Synthron/SymAsym/Hardware/Black_Devil/black_devil.kicad_pcb

## KiCad design Hardware/Black_Devil/black_devil.kicad_pcb (2023-11-16)

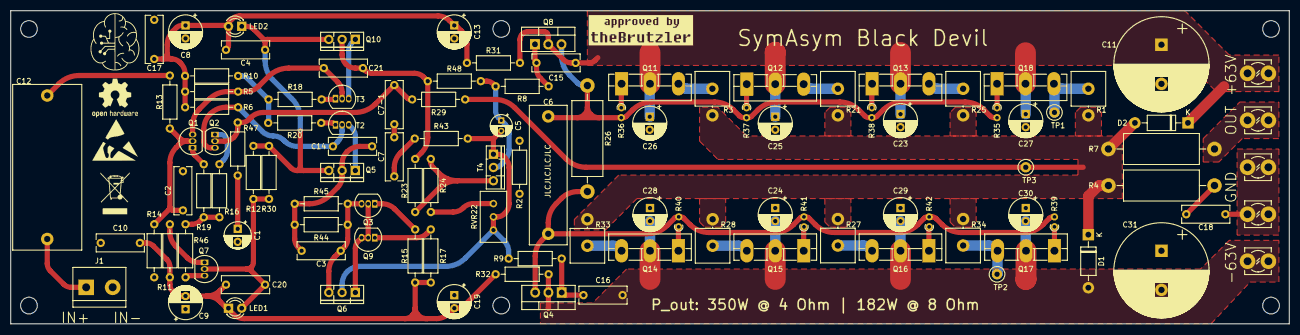
[picture p6: board black_devil.kicad_pcb from above]

Board: 2 copper layers, 245.0 x 60.0 mm, 113 parts (0 on the bottom side), 60 nets.

Parts:
C1: 330µF/16V; CP_Radial_D5.0mm_P2.50mm
C2: 680p; C_Rect_L9.0mm_W3.2mm_P7.50mm_MKT
C3, C4, C10, C17, C20: 100n; C_Rect_L9.0mm_W3.2mm_P7.50mm_MKT
C5: 47µ/25V; CP_Radial_D4.0mm_P2.00mm
C6: 680n; C_Rect_L26.5mm_W7.0mm_P22.50mm_MKS4
C7, C7-1: 10p; C_Rect_L9.0mm_W3.2mm_P7.50mm_MKT
C8, C9, C13, C19, C23, C24, C25, C26, C27, C28, C29, C30: 22µ 100V; CP_Radial_D6.3mm_P2.50mm
C11, C31: 680µ 100V; CP_Radial_D18.0mm_P7.50mm
C12: 10µ; C_Rect_L31.5mm_W13.0mm_P27.50mm_MKS4
C14, C15, C16, C21: 100p; C_Rect_L9.0mm_W3.2mm_P7.50mm_MKT
C18: 47n; C_Rect_L9.0mm_W3.2mm_P7.50mm_MKT
D1, D2: 1N4004; D_DO-41_SOD81_P10.16mm_Horizontal
J1: Input; TerminalBlock_bornier-2_P5.08mm
J3: OUT; TerminalBlock_MetzConnect_360381_1x01_Horizontal_ScrewM3.0
J4: +63V; TerminalBlock_MetzConnect_360381_1x01_Horizontal_ScrewM3.0
J5: -63V; TerminalBlock_MetzConnect_360381_1x01_Horizontal_ScrewM3.0
J6: GND; TerminalBlock_MetzConnect_360381_1x01_Horizontal_ScrewM3.0
J7: SPK_GND; TerminalBlock_MetzConnect_360381_1x01_Horizontal_ScrewM3.0
LED1: RED; LED_D3.0mm
LED2: BLUE; LED_D3.0mm
Q1, Q2, Q3, Q7, Q9: 2N5551; TO-92_Inline
Q4: MJE15031; TO-220-3_Vertical
Q5, Q10: MJE350; TO-126-3_Vertical
Q6: MJE340; TO-126-3_Vertical
Q8: MJE15030; TO-220-3_Vertical
Q11, Q12, Q13, Q18: MJL3281; TO-3PB-3_Vertical
Q14, Q15, Q16, Q17: MJL1302; TO-3PB-3_Vertical
R1, R3, R21, R25, R27, R28, R33, R34: 0R22 5W; R_Axial_Power_L20.0mm_W6.4mm_P5.08mm_Vertical
R2: 10; R_Axial_DIN0207_L6.3mm_D2.5mm_P10.16mm_Horizontal
R4: 4R7 2W; R_Axial_DIN0614_L14.3mm_D5.7mm_P20.32mm_Horizontal
R5, R6: 1k; R_Axial_DIN0207_L6.3mm_D2.5mm_P10.16mm_Horizontal
R7: 10 2W; R_Axial_DIN0614_L14.3mm_D5.7mm_P20.32mm_Horizontal
R8, R9, R18, R20: 22; R_Axial_DIN0207_L6.3mm_D2.5mm_P10.16mm_Horizontal
R10: 120; R_Axial_DIN0207_L6.3mm_D2.5mm_P10.16mm_Horizontal
R11: 390; R_Axial_DIN0207_L6.3mm_D2.5mm_P10.16mm_Horizontal
R12, R30: 68k; R_Axial_DIN0207_L6.3mm_D2.5mm_P10.16mm_Horizontal
R13: 680; R_Axial_DIN0207_L6.3mm_D2.5mm_P10.16mm_Horizontal
R14, R29, R45: 22k; R_Axial_DIN0207_L6.3mm_D2.5mm_P10.16mm_Horizontal
R15, R17: 100; R_Axial_DIN0207_L6.3mm_D2.5mm_P10.16mm_Horizontal
R16, R19, R31, R32: 47; R_Axial_DIN0207_L6.3mm_D2.5mm_P10.16mm_Horizontal
R23: 1k5; R_Axial_DIN0207_L6.3mm_D2.5mm_P10.16mm_Horizontal
R24: 270; R_Axial_DIN0207_L6.3mm_D2.5mm_P10.16mm_Horizontal
R26: 68 2W; R_Axial_DIN0614_L14.3mm_D5.7mm_P20.32mm_Horizontal
R35, R36, R37, R38, R39, R40, R41, R42: 4R7; R_Axial_DIN0204_L3.6mm_D1.6mm_P1.90mm_Vertical
R43: 470; R_Axial_DIN0207_L6.3mm_D2.5mm_P10.16mm_Horizontal
R44: 15k; R_Axial_DIN0207_L6.3mm_D2.5mm_P10.16mm_Horizontal
R46: 10k; R_Axial_DIN0207_L6.3mm_D2.5mm_P10.16mm_Horizontal
R47: 820; R_Axial_DIN0207_L6.3mm_D2.5mm_P10.16mm_Horizontal
R48: 15; R_Axial_DIN0207_L6.3mm_D2.5mm_P10.16mm_Horizontal
RVR22: 500; Potentiometer_Bourns_3296W_Vertical
T2, T3: 2N5401; TO-92_Inline
T4: BD139; TO-126-3_Vertical
TP1: MP1; TestPoint_Loop_D2.50mm_Drill1.0mm
TP2, TP3: MP2; TestPoint_Loop_D2.50mm_Drill1.0mm

Connections:
+VDC: C11.1, C15.1, C23.1, C25.1, C26.1, C27.1, D2.1 (K), J4.1, Q8.2 (C), Q11.2 (C), Q12.2 (C), Q13.2 (C), Q18.2 (C), R31.2
-VDC: C16.2, C24.2, C28.2, C29.2, C30.2, C31.2, D1.2 (A), J5.1, Q4.2 (C), Q14.2 (C), Q15.2 (C), Q16.2 (C), Q17.2 (C), R32.2
/out: J3.1, R7.2
GND: C11.2, C18.2, C23.2, C24.1, C25.2, C26.2, C27.2, C28.1, C29.1, C30.1, C31.1, J6.1, J7.1, R2.2
GNDA: C1.2, C2.2, C8.2, C9.1, C10.1, C13.2, C17.2, C19.1, J1.2, R2.1, R14.2
unnamed: C1.1, R47.1
unnamed: C7.1, C7-1.2
unnamed: C7.2, R43.1
unnamed: C12.2, R13.1
unnamed: C18.1, R4.2
unnamed: D1.1 (K), D2.2 (A), R1.2, R3.2, R4.1, R7.1, R21.2, R25.2, R27.2, R28.2, R29.2, R33.2, R34.2, TP3.1
unnamed: C12.1, J1.1
unnamed: C20.1, LED1.2 (A), Q7.2 (B), R12.2, R30.2
unnamed: C9.2, C10.2, C19.2, C20.2, LED1.1 (K), R11.2, R15.2, R17.2, R32.1
unnamed: C4.1, C8.1, C13.1, C17.1, LED2.2 (A), R5.1, R6.1, R10.1, R31.1
unnamed: C4.2, LED2.1 (K), Q5.3 (B), Q10.3 (B), R12.1, R30.1
unnamed: C2.1, Q1.2 (B), R13.2, R14.1
unnamed: C21.1, Q1.3 (C), R5.2, T3.2 (B)
unnamed: Q1.1 (E), R19.1
unnamed: C7-1.1, Q2.2 (B), R29.1, R47.2
unnamed: C14.1, Q2.3 (C), R6.2, T2.2 (B)
unnamed: Q2.1 (E), R16.1
unnamed: Q3.2 (B), Q6.1 (E), Q9.2 (B), Q9.3 (C)
unnamed: C3.2, Q3.3 (C), Q6.3 (B), R44.2, R45.2
unnamed: Q3.1 (E), R15.1
unnamed: C16.1, Q4.1 (B), R9.2
unnamed: C6.2, Q4.3 (E), R26.2, R39.2, R40.2, R41.2, R42.2
unnamed: C3.1, C14.2, Q5.2 (C), R44.1, R45.1
unnamed: Q5.1 (E), T2.3 (C)
unnamed: C5.2, Q6.2 (C), R9.1, R43.2, RVR22.2, RVR22.3, T4.1 (E)
unnamed: Q7.3 (C), R46.2
unnamed: Q7.1 (E), R11.1
unnamed: C15.2, Q8.1 (B), R8.1
unnamed: C6.1, Q8.3 (E), R26.1, R35.2, R36.2, R37.2, R38.2
unnamed: Q9.1 (E), R17.1
unnamed: C21.2, Q10.2 (C), R23.1, R48.1
unnamed: Q10.1 (E), T3.3 (C)
unnamed: Q11.1 (B), R36.1
unnamed: Q11.3 (E), R3.1
unnamed: Q12.1 (B), R37.1
unnamed: Q12.3 (E), R21.1
unnamed: Q13.1 (B), R38.1
unnamed: Q13.3 (E), R25.1
unnamed: Q14.1 (B), R40.1
unnamed: Q14.3 (E), R33.1
unnamed: Q15.1 (B), R41.1
unnamed: Q15.3 (E), R28.1
unnamed: Q16.1 (B), R42.1
unnamed: Q16.3 (E), R27.1
unnamed: Q17.1 (B), R39.1
unnamed: Q17.3 (E), R34.1, TP2.1
unnamed: Q18.1 (B), R35.1
unnamed: Q18.3 (E), R1.1, TP1.1
unnamed: R10.2, R18.1, R20.2
unnamed: R16.2, R19.2, R46.1
unnamed: R24.2, RVR22.1
unnamed: R20.1, T2.1 (E)
unnamed: R18.2, T3.1 (E)
unnamed: R23.2, R24.1, T4.3 (B)
unnamed: C5.1, R8.2, R48.2, T4.2 (C)
