Synthron/SymAsym/Hardware/Black_Devil/Softstart.kicad_pcb

## KiCad design Hardware/Black_Devil/Softstart.kicad_pcb (2023-11-16)

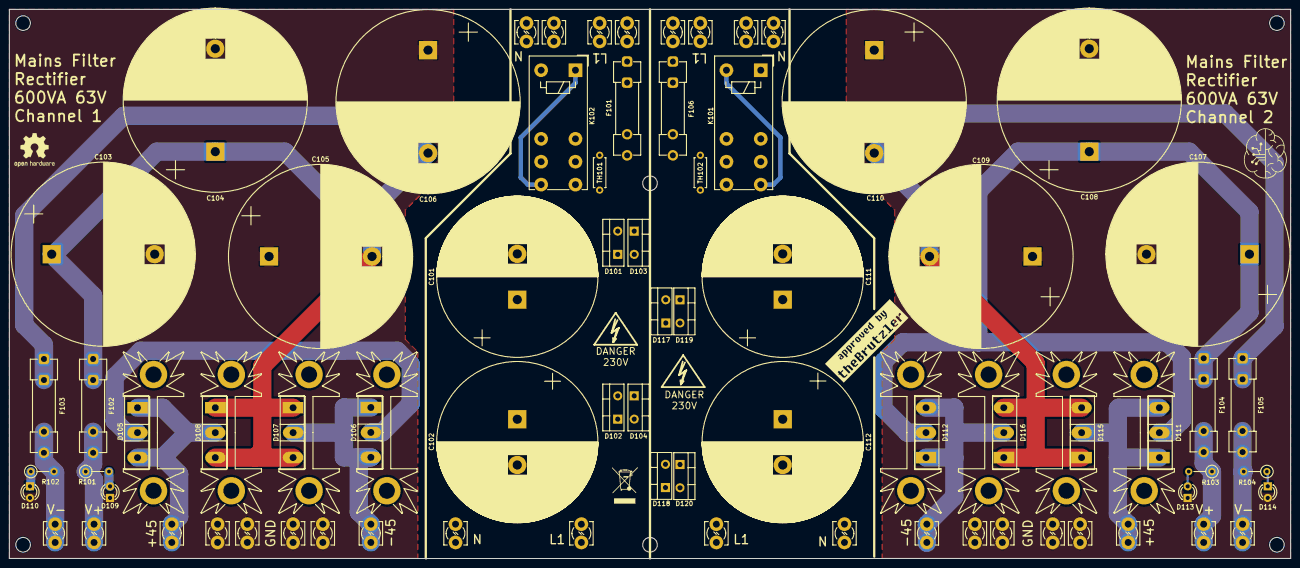
[picture p7: board Softstart.kicad_pcb from above]

Board: 2 copper layers, 280.0 x 120.0 mm, 82 parts (0 on the bottom side), 30 nets.

Parts:
C101, C102, C111, C112: 22.000µ 40V; CP_Radial_D35.0mm_P10.00mm_SnapIn
C103, C104, C105, C106, C107, C108, C109, C110: 10.000µ 80V; CP_Radial_D40.0mm_P22,5
D101, D102, D103, D104, D117, D118, D119, D120: MUR860; TO-220-2_Vertical
D105, D106, D107, D108, D111, D112, D115, D116: MUR3020; TO-247-3_Vertical
D109, D110, D113, D114: LED; LED_D3.0mm
F101, F106: 3,15A; Fuseholder_Clip-5x20mm_Littelfuse_100_Inline_P20.50x4.60mm_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
F102, F103, F104, F105: 8A; Fuseholder_Clip-5x20mm_Littelfuse_100_Inline_P20.50x4.60mm_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
HS101, HS102, HS103, HS104, HS105, HS106, HS107, HS108: SK104; Heatsink_Fischer_SK104-STCB_35x13mm__2xDrill3.5mm_ScrewM3
J101, J113, J123, J125: L1; TerminalBlock_MetzConnect_360381_1x01_Horizontal_ScrewM3.0
J102, J104, J114, J126, J127, J128: N; TerminalBlock_MetzConnect_360381_1x01_Horizontal_ScrewM3.0
J103, J124: L1_F; TerminalBlock_MetzConnect_360381_1x01_Horizontal_ScrewM3.0
J105, J116: +45VAC; TerminalBlock_MetzConnect_360381_1x01_Horizontal_ScrewM3.0
J106, J119: -45VAC; TerminalBlock_MetzConnect_360381_1x01_Horizontal_ScrewM3.0
J107, J108, J120, J121: 0V; TerminalBlock_MetzConnect_360381_1x01_Horizontal_ScrewM3.0
J109, J115: +63VDC; TerminalBlock_MetzConnect_360381_1x01_Horizontal_ScrewM3.0
J110, J122: -63VDC; TerminalBlock_MetzConnect_360381_1x01_Horizontal_ScrewM3.0
J111, J112, J117, J118: GND; TerminalBlock_MetzConnect_360381_1x01_Horizontal_ScrewM3.0
K101, K102: FINDER-40.52; Relay_DPDT_Finder_40.52
R101, R102, R103, R104: 4k7 1W; R_Axial_DIN0207_L6.3mm_D2.5mm_P5.08mm_Vertical
TH101, TH102: EPC B57364-S100; R_Axial_DIN0207_L6.3mm_D2.5mm_P7.62mm_Horizontal

Connections:
GND1: C103.2, C104.2, C105.1, C106.1, D109.1 (K), D110.2 (A), J107.1, J108.1, J111.1, J112.1
GND2: C107.2, C108.2, C109.1, C110.1, D113.1 (K), D114.2 (A), J117.1, J118.1, J120.1, J121.1
unnamed: C105.2, C106.2, D107.1 (A), D107.3 (A), D108.1 (A), D108.3 (A), F103.1
unnamed: C109.2, C110.2, D115.1 (A), D115.3 (A), D116.1 (A), D116.3 (A), F105.1
unnamed: C101.2, D101.2 (A), D103.1 (K), K102.14, K102.24, K102.A1, TH101.1
unnamed: C101.1, C102.1, D101.1 (K), D102.2 (A), D103.2 (A), D104.1 (K)
unnamed: C102.2, D102.1 (K), D104.2 (A), J103.1
unnamed: C103.1, C104.1, D105.2 (K), D106.2 (K), F102.1
unnamed: D106.1 (A), D106.3 (A), D107.2 (K), J106.1
unnamed: D105.1 (A), D105.3 (A), D108.2 (K), J105.1
unnamed: D109.2 (A), R101.2
unnamed: D110.1 (K), R102.1
unnamed: C107.1, C108.1, D111.2 (K), D112.2 (K), F104.1
unnamed: D113.2 (A), R103.2
unnamed: D114.1 (K), R104.1
unnamed: D111.1 (A), D111.3 (A), D115.2 (K), J116.1
unnamed: D112.1 (A), D112.3 (A), D116.2 (K), J119.1
unnamed: C111.2, D117.2 (A), D119.1 (K), K101.14, K101.24, K101.A2, TH102.1
unnamed: C111.1, C112.1, D117.1 (K), D118.2 (A), D119.2 (A), D120.1 (K)
unnamed: C112.2, D118.1 (K), D120.2 (A), J124.1
unnamed: F101.2, K102.11, K102.21, TH101.2
unnamed: F106.2, K101.11, K101.21, TH102.2
unnamed: F101.1, J101.1, J113.1
unnamed: J102.1, J104.1, J114.1, K102.A2
unnamed: F102.2, J109.1, R101.1
unnamed: F103.2, J110.1, R102.2
unnamed: F104.2, J115.1, R103.1
unnamed: F105.2, J122.1, R104.2
unnamed: F106.1, J123.1, J125.1
unnamed: J126.1, J127.1, J128.1, K101.A1
