Synthron/SymAsym/Hardware/Black_Devil/VU-Meter.kicad_pcb

## KiCad design Hardware/Black_Devil/VU-Meter.kicad_pcb (2023-11-16)

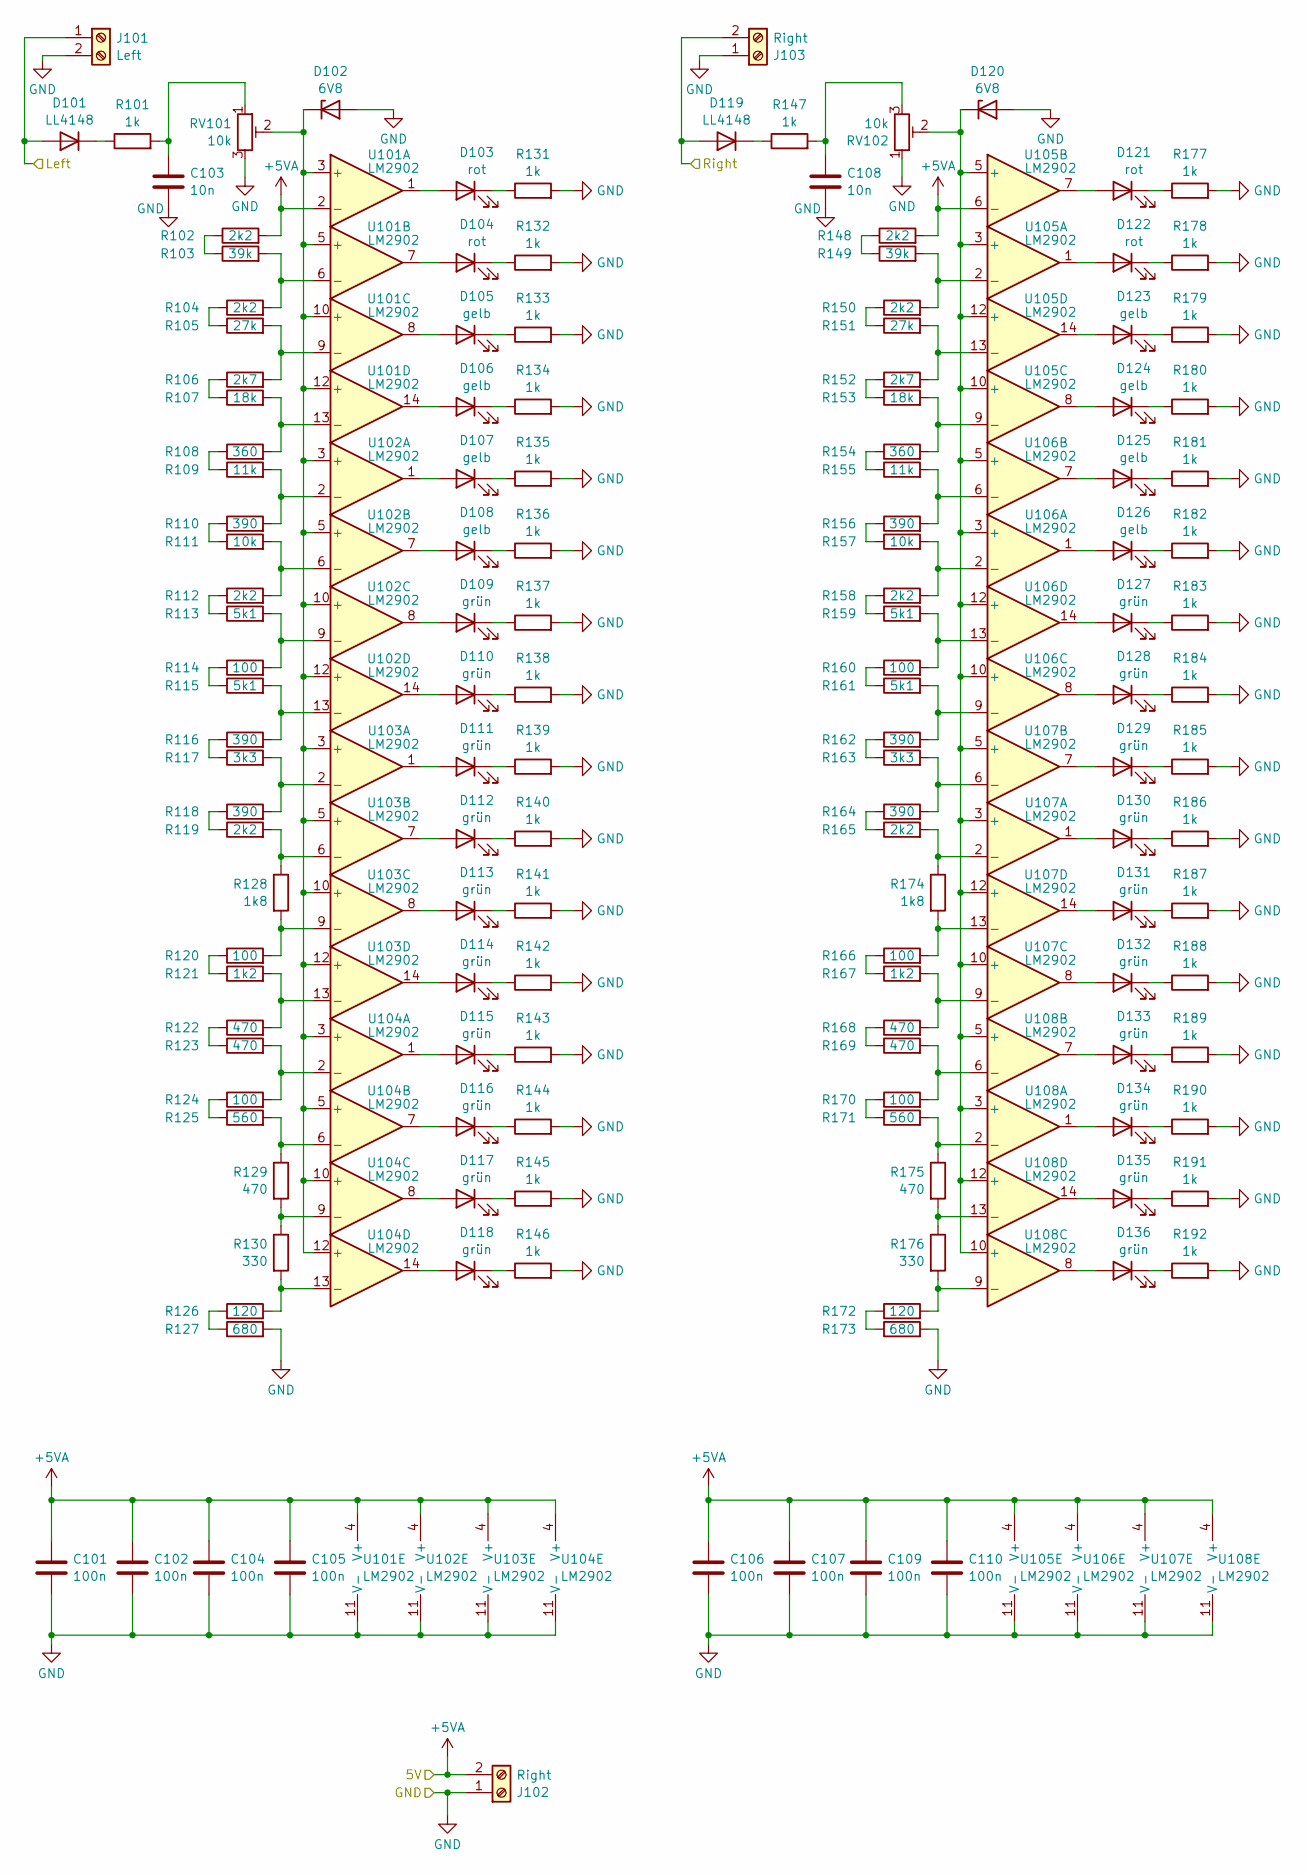
[picture p8: schematic VU-Meter.kicad_sch]

Parts:
C101, C102, C104, C105, C106, C107, C109, C110: 100n; C_0603_1608Metric
C103, C108: 10n; C_0603_1608Metric
D101, D119: LL4148; D_MiniMELF
D102, D120: 6V8; D_MiniMELF
D103, D104, D121, D122: rot; LED_D3.0mm_Clear
D105, D106, D107, D108, D123, D124, D125, D126: gelb; LED_D3.0mm_Clear
D109, D110, D111, D112, D113, D114, D115, D116, D117, D118, D127, D128, D129, D130, D131, D132, D133, D134, D135, D136: grün; LED_D3.0mm_Clear
J101: Left; TerminalBlock_bornier-2_P5.08mm
J102, J103: Right; TerminalBlock_bornier-2_P5.08mm
R101, R131, R132, R133, R134, R135, R136, R137, R138, R139, R140, R141, R142, R143, R144, R145, R146, R147, R177, R178, R179, R180, R181, R182, R183, R184, R185, R186, R187, R188, R189, R190, R191, R192: 1k; R_0603_1608Metric
R102, R104, R112, R119, R148, R150, R158, R165: 2k2; R_0603_1608Metric
R103, R149: 39k; R_0603_1608Metric
R105, R151: 27k; R_0603_1608Metric
R106, R152: 2k7; R_0603_1608Metric
R107, R153: 18k; R_0603_1608Metric
R108, R154: 360; R_0603_1608Metric
R109, R155: 11k; R_0603_1608Metric
R110, R116, R118, R156, R162, R164: 390; R_0603_1608Metric
R111, R157: 10k; R_0603_1608Metric
R113, R115, R159, R161: 5k1; R_0603_1608Metric
R114, R120, R124, R160, R166, R170: 100; R_0603_1608Metric
R117, R163: 3k3; R_0603_1608Metric
R121, R167: 1k2; R_0603_1608Metric
R122, R123, R129, R168, R169, R175: 470; R_0603_1608Metric
R125, R171: 560; R_0603_1608Metric
R126, R172: 120; R_0603_1608Metric
R127, R173: 680; R_0603_1608Metric
R128, R174: 1k8; R_0603_1608Metric
R130, R176: 330; R_0603_1608Metric
RV101, RV102: 10k; Potentiometer_Vishay_TS53YJ_Vertical
U101, U102, U103, U104, U105, U106, U107, U108: LM2902; TSSOP-14_4.4x5mm_P0.65mm

Connections:
+5VA: C101.1, C102.1, C104.1, C105.1, C106.1, C107.1, C109.1, C110.1, J102.2, R102.2, R148.2, U101.2 (-), U101.4 (V+), U102.4 (V+), U103.4 (V+), U104.4 (V+), U105.4 (V+), U105.6 (-), U106.4 (V+), U107.4 (V+), U108.4 (V+)
/Left: D101.2 (A), J101.1
/Right: D119.2 (A), J103.2
GND: C101.2, C102.2, C103.2, C104.2, C105.2, C106.2, C107.2, C108.2, C109.2, C110.2, D102.2 (A), D120.2 (A), J101.2, J102.1, J103.1, R127.2, R131.2, R132.2, R133.2, R134.2, R135.2, R136.2, R137.2, R138.2, R139.2, R140.2, R141.2, R142.2, R143.2, R144.2, R145.2, R146.2, R173.2, R177.2, R178.2, R179.2, R180.2, R181.2, R182.2, R183.2, R184.2, R185.2, R186.2, R187.2, R188.2, R189.2, R190.2, R191.2, R192.2, RV101.3, RV102.1, U101.11 (V-), U102.11 (V-), U103.11 (V-), U104.11 (V-), U105.11 (V-), U106.11 (V-), U107.11 (V-), U108.11 (V-)
unnamed: C103.1, R101.2, RV101.1
unnamed: C108.1, R147.2, RV102.3
unnamed: D101.1 (K), R101.1
unnamed: D102.1 (K), RV101.2, U101.3 (+), U101.5 (+), U101.10 (+), U101.12 (+), U102.3 (+), U102.5 (+), U102.10 (+), U102.12 (+), U103.3 (+), U103.5 (+), U103.10 (+), U103.12 (+), U104.3 (+), U104.5 (+), U104.10 (+), U104.12 (+)
unnamed: D103.2 (A), U101.1
unnamed: D103.1 (K), R131.1
unnamed: D104.2 (A), U101.7
unnamed: D104.1 (K), R132.1
unnamed: D105.2 (A), U101.8
unnamed: D105.1 (K), R133.1
unnamed: D106.2 (A), U101.14
unnamed: D106.1 (K), R134.1
unnamed: D107.2 (A), U102.1
unnamed: D107.1 (K), R135.1
unnamed: D108.2 (A), U102.7
unnamed: D108.1 (K), R136.1
unnamed: D109.2 (A), U102.8
unnamed: D109.1 (K), R137.1
unnamed: D110.2 (A), U102.14
unnamed: D110.1 (K), R138.1
unnamed: D111.2 (A), U103.1
unnamed: D111.1 (K), R139.1
unnamed: D112.2 (A), U103.7
unnamed: D112.1 (K), R140.1
unnamed: D113.2 (A), U103.8
unnamed: D113.1 (K), R141.1
unnamed: D114.2 (A), U103.14
unnamed: D114.1 (K), R142.1
unnamed: D115.2 (A), U104.1
unnamed: D115.1 (K), R143.1
unnamed: D116.2 (A), U104.7
unnamed: D116.1 (K), R144.1
unnamed: D117.2 (A), U104.8
unnamed: D117.1 (K), R145.1
unnamed: D118.2 (A), U104.14
unnamed: D118.1 (K), R146.1
unnamed: D119.1 (K), R147.1
unnamed: D120.1 (K), RV102.2, U105.3 (+), U105.5 (+), U105.10 (+), U105.12 (+), U106.3 (+), U106.5 (+), U106.10 (+), U106.12 (+), U107.3 (+), U107.5 (+), U107.10 (+), U107.12 (+), U108.3 (+), U108.5 (+), U108.10 (+), U108.12 (+)
unnamed: D121.2 (A), U105.7
unnamed: D121.1 (K), R177.1
unnamed: D122.2 (A), U105.1
unnamed: D122.1 (K), R178.1
unnamed: D123.2 (A), U105.14
unnamed: D123.1 (K), R179.1
unnamed: D124.2 (A), U105.8
unnamed: D124.1 (K), R180.1
unnamed: D125.2 (A), U106.7
unnamed: D125.1 (K), R181.1
unnamed: D126.2 (A), U106.1
unnamed: D126.1 (K), R182.1
unnamed: D127.2 (A), U106.14
unnamed: D127.1 (K), R183.1
unnamed: D128.2 (A), U106.8
unnamed: D128.1 (K), R184.1
unnamed: D129.2 (A), U107.7
unnamed: D129.1 (K), R185.1
unnamed: D130.2 (A), U107.1
unnamed: D130.1 (K), R186.1
unnamed: D131.2 (A), U107.14
unnamed: D131.1 (K), R187.1
unnamed: D132.2 (A), U107.8
unnamed: D132.1 (K), R188.1
unnamed: D133.2 (A), U108.7
unnamed: D133.1 (K), R189.1
unnamed: D134.2 (A), U108.1
unnamed: D134.1 (K), R190.1
unnamed: D135.2 (A), U108.14
unnamed: D135.1 (K), R191.1
unnamed: D136.2 (A), U108.8
unnamed: D136.1 (K), R192.1
unnamed: R102.1, R103.1
unnamed: R104.1, R105.1
unnamed: R106.1, R107.1
unnamed: R108.1, R109.1
unnamed: R110.1, R111.1
unnamed: R112.1, R113.1
unnamed: R114.1, R115.1
unnamed: R116.1, R117.1
unnamed: R118.1, R119.1
unnamed: R120.1, R121.1
unnamed: R122.1, R123.1
unnamed: R124.1, R125.1
unnamed: R126.1, R127.1
unnamed: R148.1, R149.1
unnamed: R150.1, R151.1
unnamed: R152.1, R153.1
unnamed: R154.1, R155.1
unnamed: R156.1, R157.1
unnamed: R158.1, R159.1
unnamed: R160.1, R161.1
unnamed: R162.1, R163.1
unnamed: R164.1, R165.1
unnamed: R166.1, R167.1
unnamed: R168.1, R169.1
unnamed: R170.1, R171.1
unnamed: R172.1, R173.1
unnamed: R103.2, R104.2, U101.6 (-)
unnamed: R105.2, R106.2, U101.9 (-)
unnamed: R107.2, R108.2, U101.13 (-)
unnamed: R109.2, R110.2, U102.2 (-)
unnamed: R111.2, R112.2, U102.6 (-)
unnamed: R113.2, R114.2, U102.9 (-)
unnamed: R115.2, R116.2, U102.13 (-)
unnamed: R117.2, R118.2, U103.2 (-)
unnamed: R119.2, R128.1, U103.6 (-)
unnamed: R120.2, R128.2, U103.9 (-)
unnamed: R121.2, R122.2, U103.13 (-)
unnamed: R123.2, R124.2, U104.2 (-)
unnamed: R125.2, R129.1, U104.6 (-)
unnamed: R129.2, R130.1, U104.9 (-)
unnamed: R126.2, R130.2, U104.13 (-)
unnamed: R149.2, R150.2, U105.2 (-)
unnamed: R153.2, R154.2, U105.9 (-)
unnamed: R151.2, R152.2, U105.13 (-)
unnamed: R157.2, R158.2, U106.2 (-)
unnamed: R155.2, R156.2, U106.6 (-)
unnamed: R161.2, R162.2, U106.9 (-)
unnamed: R159.2, R160.2, U106.13 (-)
unnamed: R165.2, R174.1, U107.2 (-)
unnamed: R163.2, R164.2, U107.6 (-)
unnamed: R167.2, R168.2, U107.9 (-)
unnamed: R166.2, R174.2, U107.13 (-)
unnamed: R171.2, R175.1, U108.2 (-)
unnamed: R169.2, R170.2, U108.6 (-)
unnamed: R172.2, R176.2, U108.9 (-)
unnamed: R175.2, R176.1, U108.13 (-)

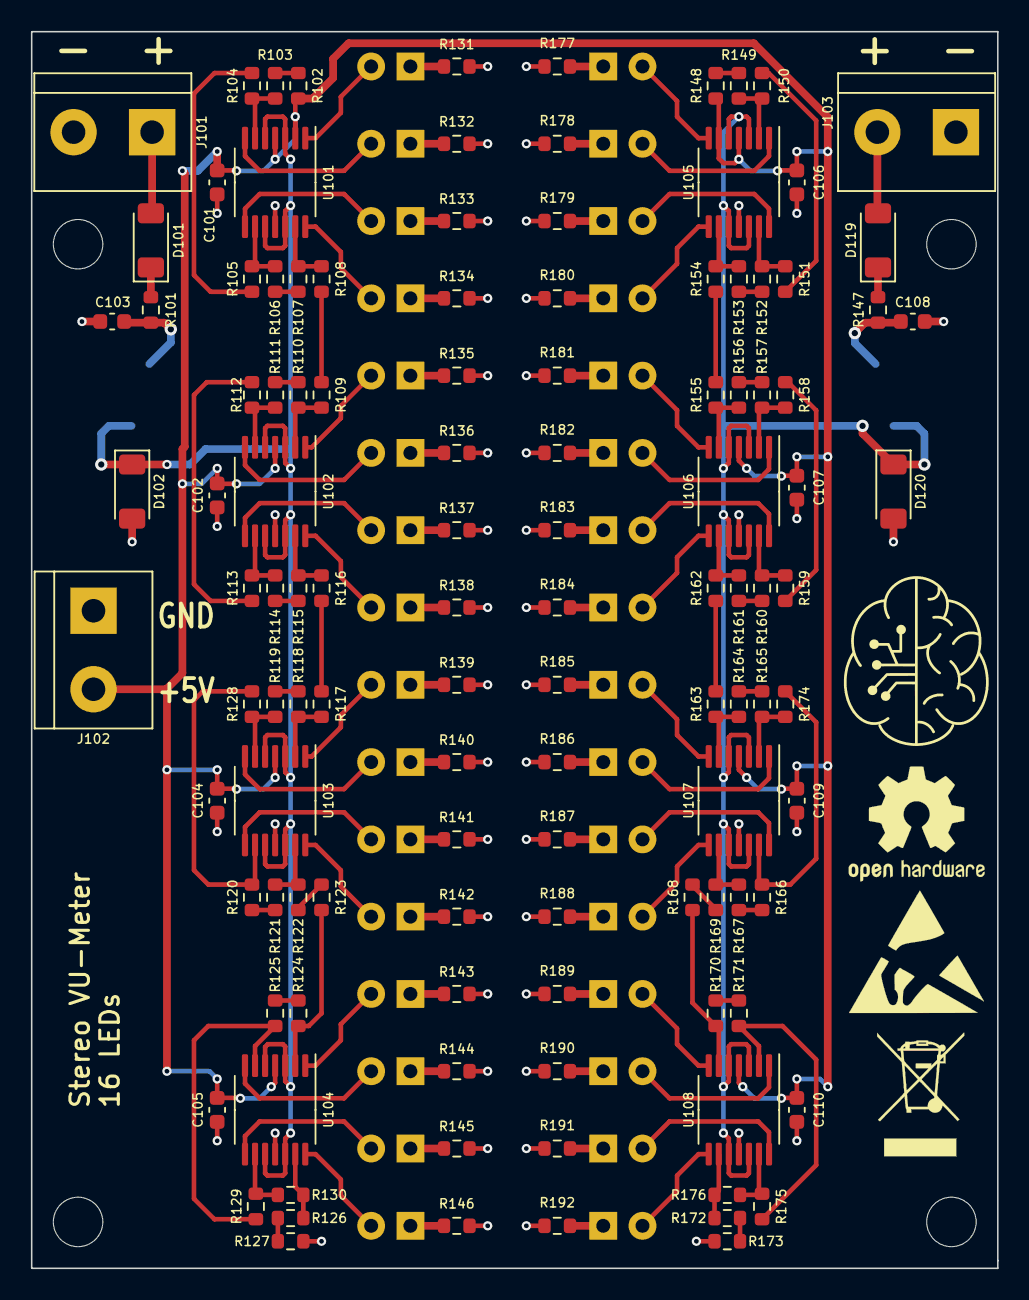
[picture p9: board VU-Meter.kicad_pcb from above]

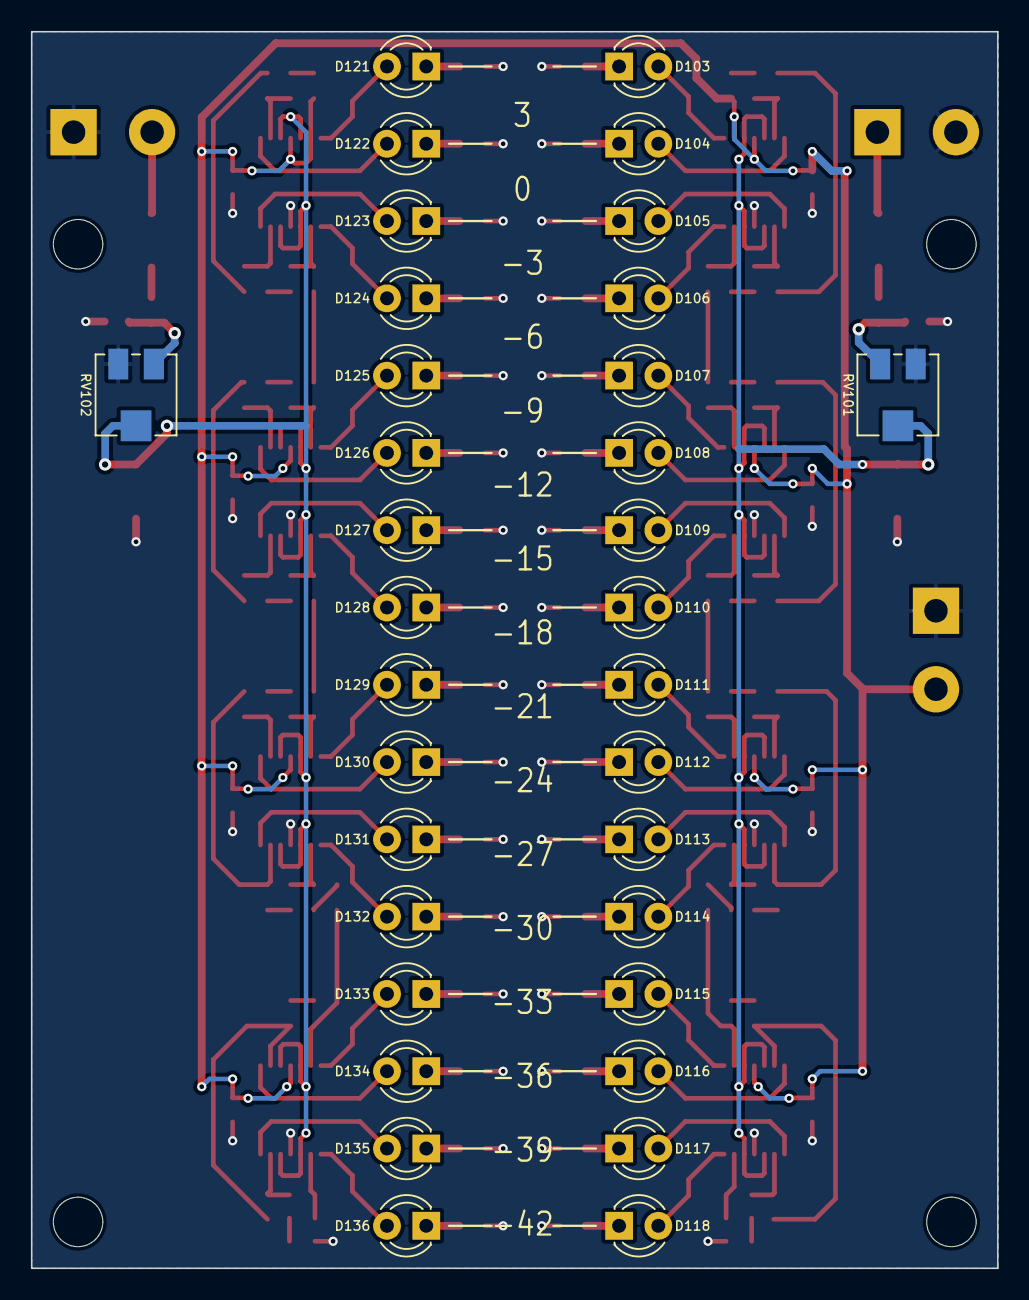
[picture p10: board VU-Meter.kicad_pcb from below]

Board: 2 copper layers, 62.5 x 80.0 mm, 151 parts (34 on the bottom side), 130 nets.
