Synthron/SymAsym/Hardware/Black_Devil/digital.kicad_pcb

## KiCad design Hardware/Black_Devil/digital.kicad_pcb (2023-11-16)

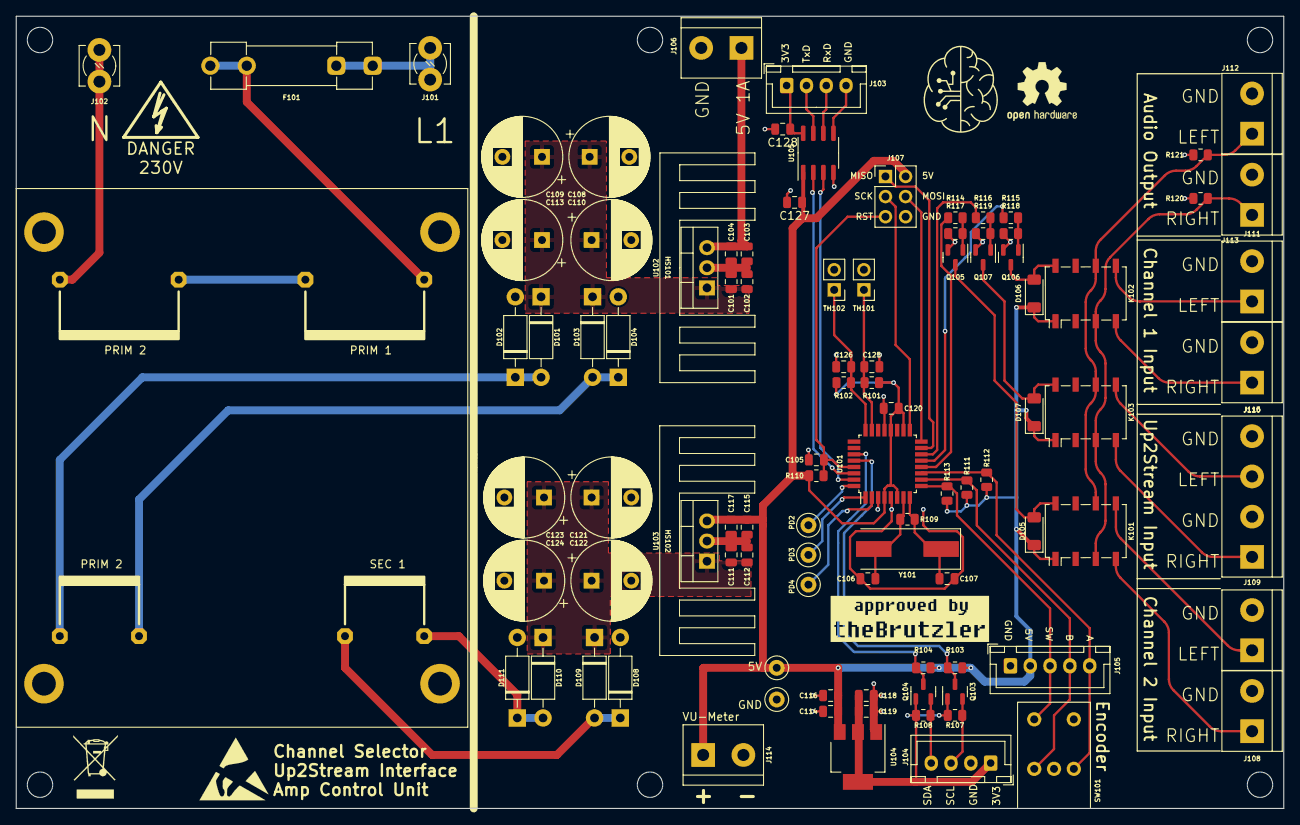
[picture p11: board digital.kicad_pcb from above]

Board: 2 copper layers, 160.0 x 100.0 mm, 99 parts (0 on the bottom side), 56 nets.

Parts:
C101, C104, C111, C114, C117, C119, C125, C126: 1µ; C_0805_2012Metric
C102, C103, C105, C112, C115, C116, C118, C120, C127, C128: 100n; C_0805_2012Metric
C106, C107: 18p; C_0805_2012Metric
C108, C109, C110, C113, C121, C122, C123, C124: 470µ; CP_Radial_D10.0mm_P5.00mm
D101, D102, D103, D104, D108, D109, D110, D111: 1N4004; D_DO-41_SOD81_P10.16mm_Horizontal
D105, D106, D107: LL4148; D_MiniMELF
F101: 0,5A; Fuseholder_Clip-5x20mm_Littelfuse_100_Inline_P20.50x4.60mm_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
HS101, HS102: Heatsink; V 4330N
J101: L1; TerminalBlock_MetzConnect_360381_1x01_Horizontal_ScrewM3.0
J102: N; TerminalBlock_MetzConnect_360381_1x01_Horizontal_ScrewM3.0
J103, J104: OLED; JST_XH_B4B-XH-A_1x04_P2.50mm_Vertical
J105: Encoder; JST_XH_B5B-XH-A_1x05_P2.50mm_Vertical
J106: Up2Stream; TerminalBlock_bornier-2_P5.08mm
J107: ICSP; PinHeader_2x03_P2.54mm_Vertical
J108: Klinke_Right; TerminalBlock_bornier-2_P5.08mm
J109: Klinke_Links; TerminalBlock_bornier-2_P5.08mm
J110: Cinch_Right; TerminalBlock_bornier-2_P5.08mm
J111: Cinch_Left; TerminalBlock_bornier-2_P5.08mm
J112: Left; TerminalBlock_bornier-2_P5.08mm
J113: Right; TerminalBlock_bornier-2_P5.08mm
J114: VU-Meter; TerminalBlock_bornier-2_P5.08mm
J115: Up2Stream; TerminalBlock_bornier-4_P5.08mm
K101, K102, K103: G6K-2; Relay_DPDT_Omron_G6K-2F
Q103, Q104, Q105, Q106, Q107: BSS138; SOT-23
R101, R102, R103, R104, R107, R108: 4k7; R_0805_2012Metric
R109: 1M; R_0805_2012Metric
R110, R111, R112, R113, R114, R115, R116: 10k; R_0805_2012Metric
R117, R118, R119: 100k; R_0805_2012Metric
R120, R121: 470k; R_0805_2012Metric
SW101: RotaryEncoder_Switch; RotaryEncoder_Bourns_Horizontal_PEC09-2xxxF-Sxxxx
TH101, TH102: Thermistor_NTC; PinHeader_1x02_P2.54mm_Vertical
TP101: PD2; TestPoint_Loop_D2.50mm_Drill1.0mm
TP102: PD3; TestPoint_Loop_D2.50mm_Drill1.0mm
TP103: PD4; TestPoint_Loop_D2.50mm_Drill1.0mm
TP104, TP105: TestPoint; TestPoint_Loop_D2.50mm_Drill1.0mm
TR101: UI 39/10,2 209; BLOCK 14VA
U101: ATmega328P-A; TQFP-32_7x7mm_P0.8mm
U102, U103: L7805; TO-220-3_Vertical
U104: AP1117-33; SOT-223-3_TabPin2
U105: ADuM1201AR; SOIC-8_3.9x4.9mm_P1.27mm
Y101: 16MHz; Crystal_SMD_HC49-SD

Connections:
+3V3: C118.1, C119.1, J104.1, Q103.1 (G), Q104.1 (G), R107.1, R108.1, U104.2 (VO)
+5V: C114.1, C115.1, C116.1, C117.1, C120.1, C127.1, D105.1 (K), D106.1 (K), D107.1 (K), J105.2, J107.2, J114.1, K101.1, K102.1, K103.1, R101.1, R102.2, R103.1, R104.1, R110.1, R111.1, R112.1, R113.1, TP105.1, U101.4 (VCC), U101.6 (VCC), U101.18 (AVCC), U101.20 (AREF), U103.3 (OUT), U104.3 (VI), U105.1 (VDD1)
+5VA: C103.1, C104.1, J106.1, U102.3 (OUT)
+12V: C111.1, C112.1, C121.1, C122.1, C123.1, C124.1, D108.1 (K), D110.1 (K), U103.1 (IN)
+12VA: C101.1, C102.1, C108.1, C109.1, C110.1, C113.1, D101.1 (K), D103.1 (K), U102.1 (IN)
/L1: F101.1, J101.1
/Left: J112.1, K101.6, K102.6, K103.6, R121.1
/N: J102.1, TR101.4
/Right: J113.1, K101.3, K102.3, K103.3, R120.1
/Sig_GND: J108.2, J109.2, J110.2, J111.2, J112.2, J113.2, J115.2, J115.4, R120.2, R121.2
GND: C105.2, C106.1, C107.1, C111.2, C112.2, C114.2, C115.2, C116.2, C117.2, C118.2, C119.2, C120.2, C121.2, C122.2, C123.2, C124.2, C125.1, C126.2, C127.2, D109.2 (A), D111.2 (A), J104.2, J105.1, J107.6, J114.2, Q105.2 (S), Q106.2 (S), Q107.2 (S), R117.2, R118.2, R119.2, SW101.C, SW101.S2, TH101.2, TH102.2, TP104.1, U101.3 (GND), U101.5 (GND), U101.21 (GND), U103.2 (GND), U104.1 (GND), U105.4 (GND1)
GND1: C101.2, C102.2, C103.2, C104.2, C108.2, C109.2, C110.2, C113.2, C128.2, D102.2 (A), D104.2 (A), J103.4, J106.2, U102.2 (GND), U105.5 (GND2)
MISO: J107.1, U101.15 (PB3)
MOSI: J107.4, U101.16 (PB4)
NTC1: C125.2, R101.2, TH101.1, U101.23 (PC0)
NTC2: C126.1, R102.1, TH102.1, U101.24 (PC1)
unnamed: D101.2 (A), D102.1 (K), TR101.8
unnamed: D103.2 (A), D104.1 (K), TR101.7
unnamed: D105.2 (A), K101.8, Q105.3 (D)
unnamed: D106.2 (A), K102.8, Q106.3 (D)
unnamed: D107.2 (A), K103.8, Q107.3 (D)
unnamed: D108.2 (A), D109.1 (K), TR101.6
unnamed: D110.2 (A), D111.1 (K), TR101.5
unnamed: F101.2, TR101.1
unnamed: C128.1, J103.1, U105.8 (VDD2)
unnamed: J103.2, U105.7 (VIA)
unnamed: J103.3, U105.6 (VOB)
unnamed: J104.3, Q103.2 (S), R107.2
unnamed: J104.4, Q104.2 (S), R108.2
unnamed: J105.3, R113.2, SW101.S1, U101.9 (PD5)
unnamed: J105.4, R111.2, SW101.A, U101.10 (PD6)
unnamed: J105.5, R112.2, SW101.B, U101.11 (PD7)
unnamed: J108.1, K101.4
unnamed: J109.1, K101.5
unnamed: J110.1, K102.4
unnamed: J111.1, K102.5
unnamed: J115.1, K103.4
unnamed: J115.3, K103.5
unnamed: Q105.1 (G), R114.2, R117.1
unnamed: Q106.1 (G), R115.2, R118.1
unnamed: Q107.1 (G), R116.2, R119.1
unnamed: TR101.2, TR101.3
unnamed: R114.1, U101.12 (PB0)
unnamed: R115.1, U101.13 (PB1)
unnamed: R116.1, U101.14 (PB2)
unnamed: TP101.1, U101.32 (PD2)
unnamed: TP102.1, U101.1 (PD3)
unnamed: TP103.1, U101.2 (PD4)
unnamed: C106.2, R109.1, U101.7 (XTAL1/PB6), Y101.2
unnamed: C107.2, R109.2, U101.8 (XTAL2/PB7), Y101.1
RST: C105.1, J107.5, R110.2, U101.29 (~RESET/PC6)
RxD: U101.30 (PD0), U105.2 (VOA)
SCK: J107.3, U101.17 (PB5)
SCL: Q103.3 (D), R103.2, U101.28 (PC5)
SDA: Q104.3 (D), R104.2, U101.27 (PC4)
TxD: U101.31 (PD1), U105.3 (VIB)
